vetschn/ohmcoder/auxiliary/spice/env_follower.asc

B1: bv; V=V(amplitude)*V(program)
C1: cap; 680n
C2: cap; 680n
D1: diode; 1N4148
D2: diode; 1N4148
R1: res2; 10k
R2: res2; 10k
R3: res2; 10k
R4: res2; 10k
R5: res2; 10k
R6: res2; 10k
R7: res2; 100k
R8: res2; 100k
U1: TL074
U2: TL074
U3: TL074
V1: voltage; SINE(0 1 100)
V2: voltage; 12
V3: voltage; -12
V4: voltage; SINE(0.5 0.5 2)
Named nets: 0, +12V, -12V, amplitude, program, IN, ENV
.tran 10u 1
