vetschn/ohmcoder/auxiliary/spice/filter.asc

C1: cap; {c}
C2: cap; {c}
C3: cap; {c}
C4: cap; {c}
R1: res; 33k
R2: res; 2k
R3: res; 200k
R4: res; 20k
R5: res; 1.2k
R6: res; 120k
U1: TL074
U2: TL074
V1: voltage; ""; AC 1
V2: voltage; 12
V3: voltage; -12
Named nets: 0, 12V, -12V
.step param c list 0.91n 1.3n 1.8n 2.4n 3.3n 4.7n 6.8n 9.1n 13n 18n 24n 33n 47n 68n 91n 130n
.ac dec 1000 1 100000
